etemu/wilssen/core/PCB/temp/microSD_pin.png

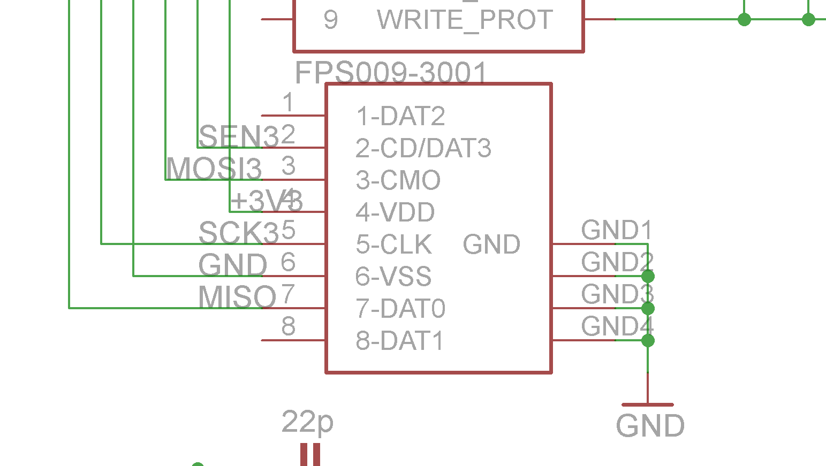
core/PCB/temp/microSD_pin.png
