etemu/wilssen/core/PCB/Wilssen_core_v0.201a.brd.png

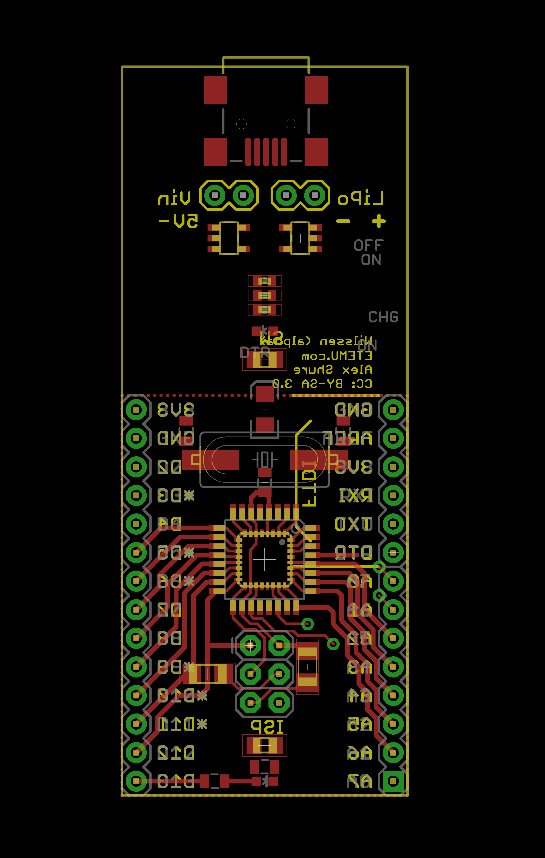
core/PCB/Wilssen_core_v0.201a.brd.png
