etemu/wilssen/core/PCB/Wilssen_core_v0.203a.brd.png

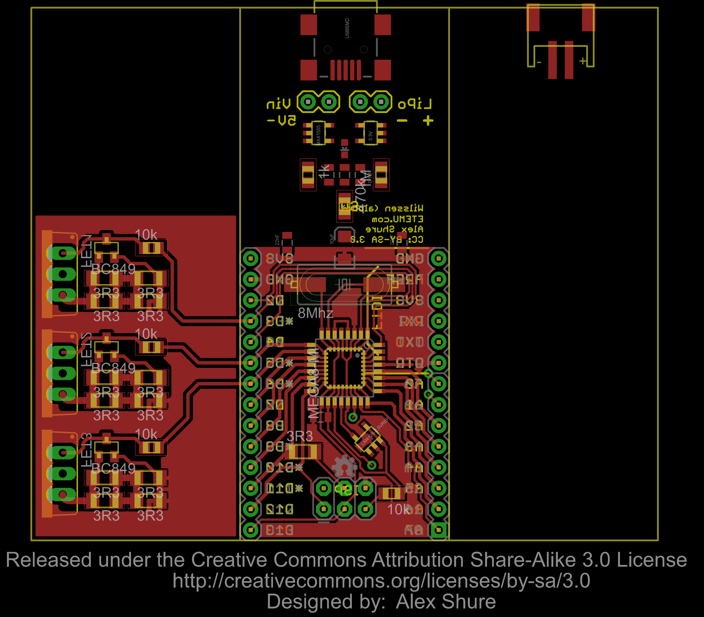
core/PCB/Wilssen_core_v0.203a.brd.png
