etemu/wilssen/core/PCB/Wilssen_core_v0.203a.brd_detail.png

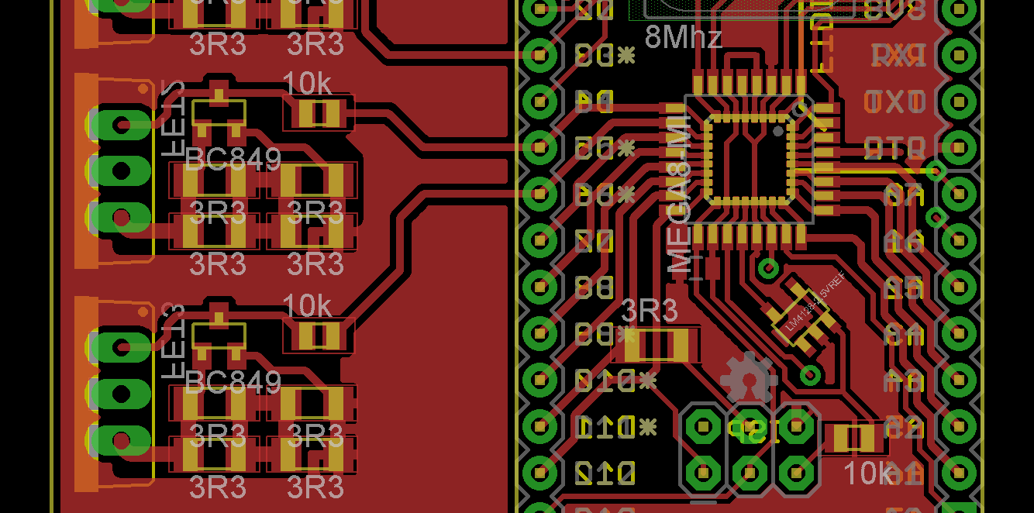
core/PCB/Wilssen_core_v0.203a.brd_detail.png
