etemu/wilssen/core/PCB/Wilssen_core_v0.203a.sch.png

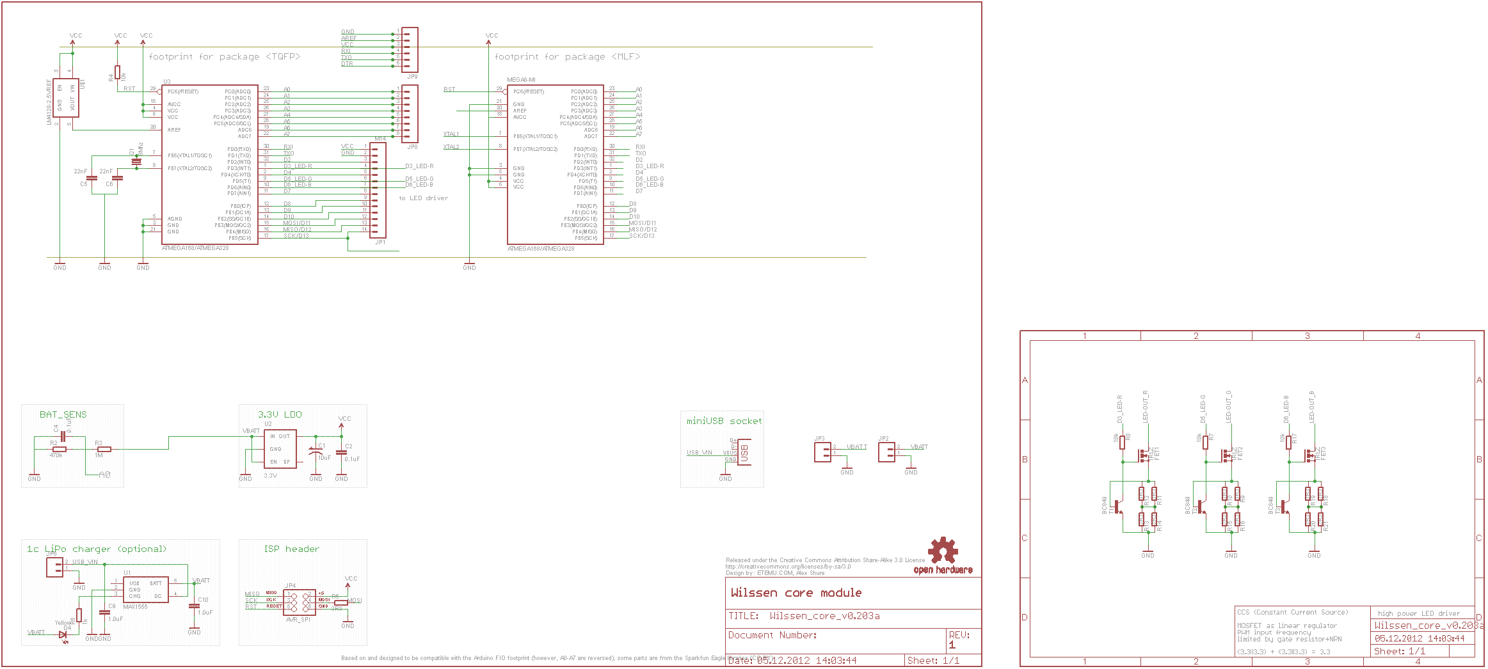
core/PCB/Wilssen_core_v0.203a.sch.png
