etemu/wilssen/core/PCB/Wilssen_core_v0.204a.brd.png

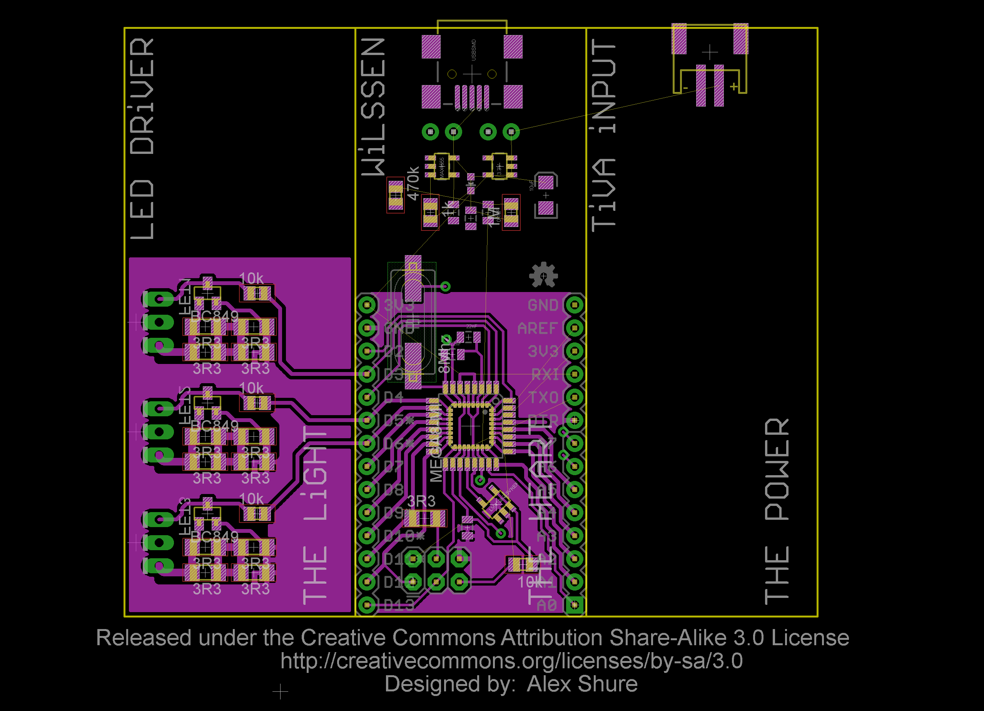
core/PCB/Wilssen_core_v0.204a.brd.png
