etemu/wilssen/core/PCB/Wilssen_core_v0.204a.brd_detail.png

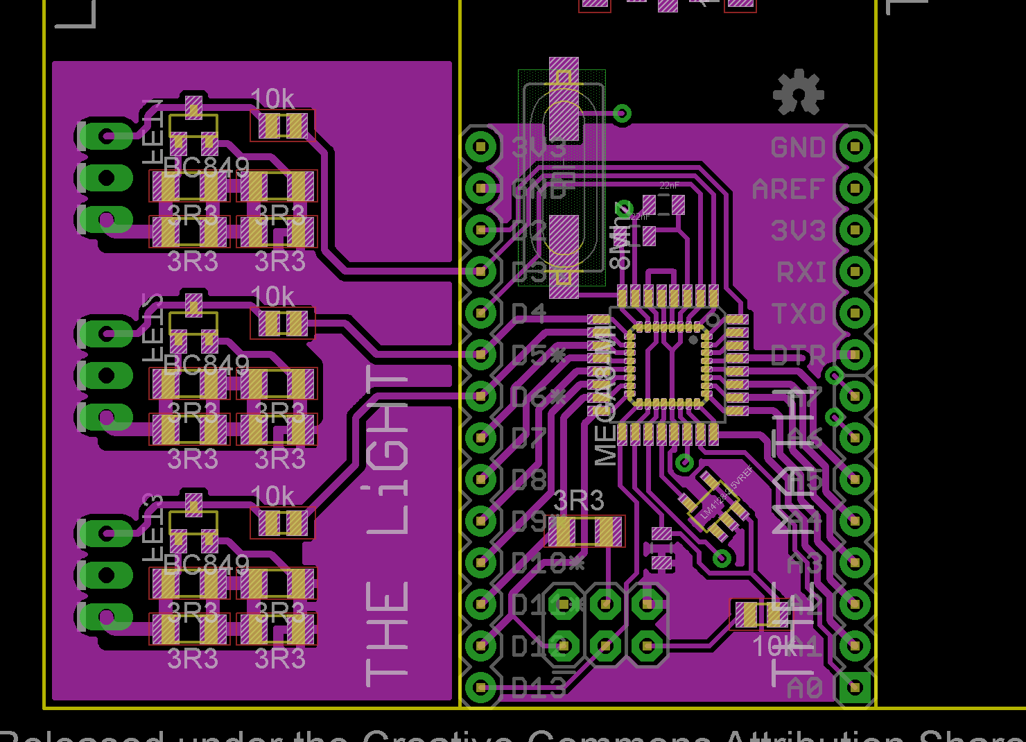
core/PCB/Wilssen_core_v0.204a.brd_detail.png
