etemu/wilssen/core/PCB/Wilssen_core_v0.206a.brd.png

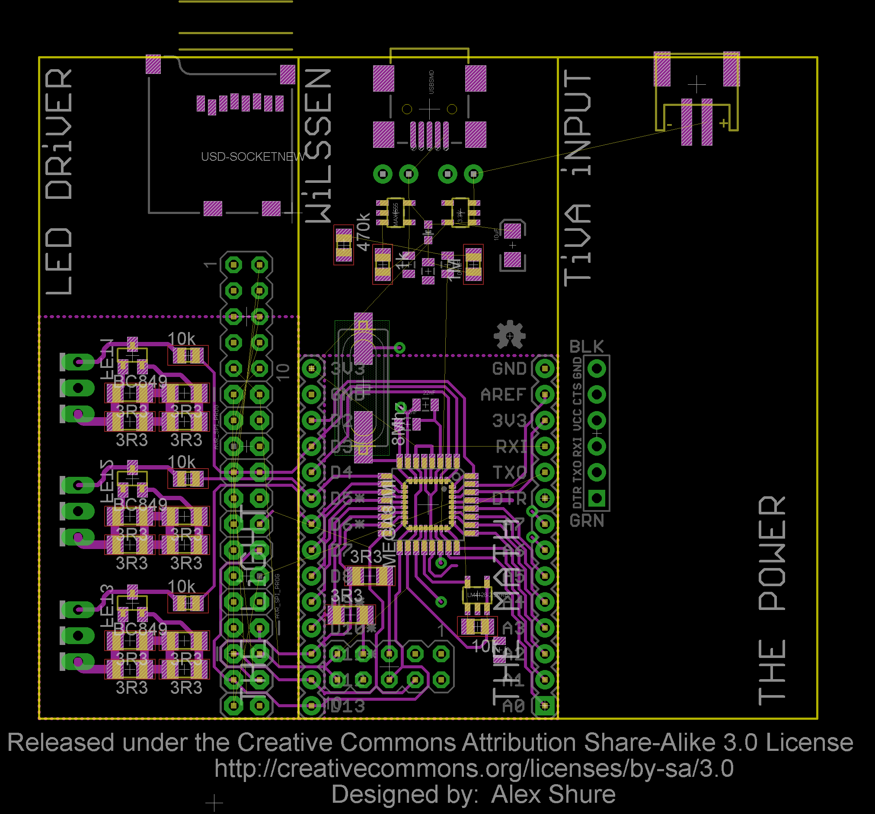
core/PCB/Wilssen_core_v0.206a.brd.png
