etemu/wilssen/core/PCB/Wilssen_core_v0.209a.brd.png

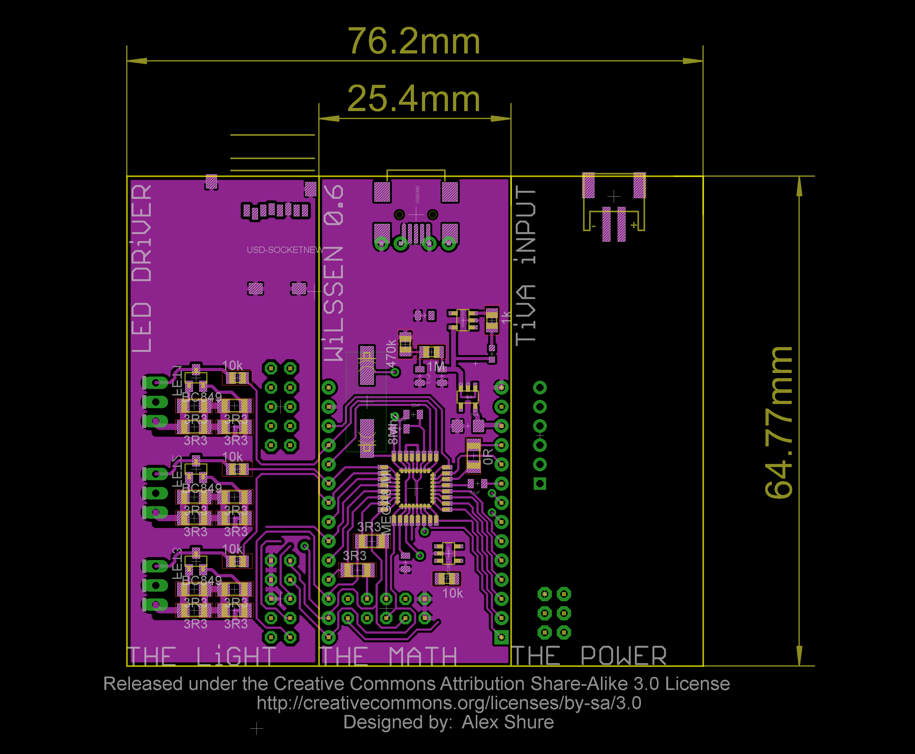
core/PCB/Wilssen_core_v0.209a.brd.png
