etemu/wilssen/core/PCB/Wilssen_core_v0.215a.brd.png

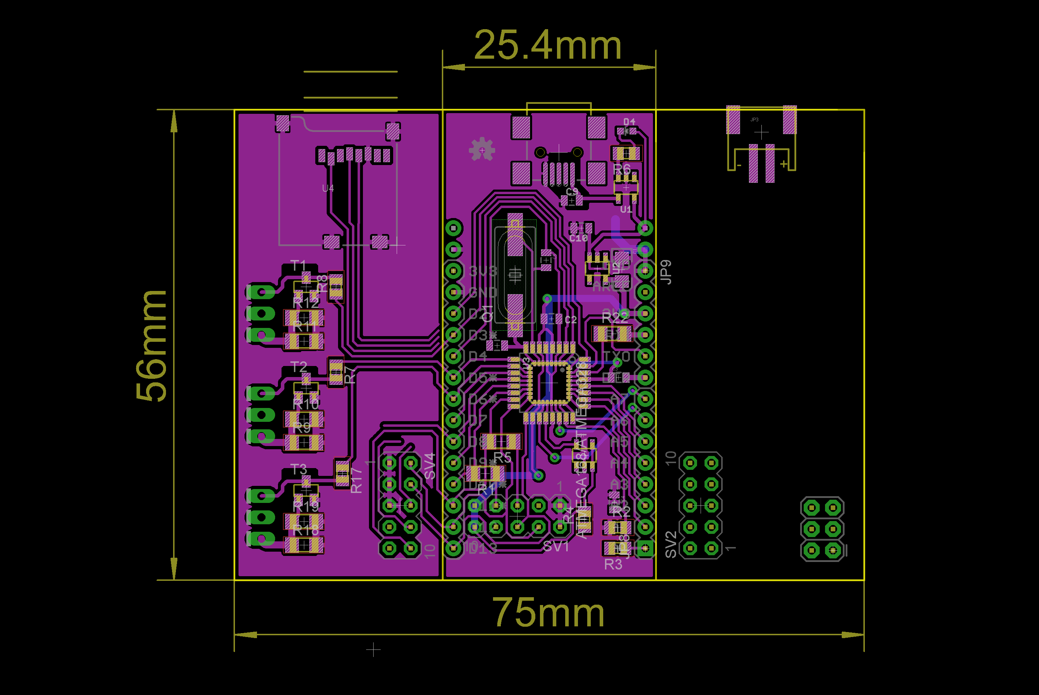
core/PCB/Wilssen_core_v0.215a.brd.png
