etemu/wilssen/core/PCB/Wilssen_core_v0.215a_2.brd.png

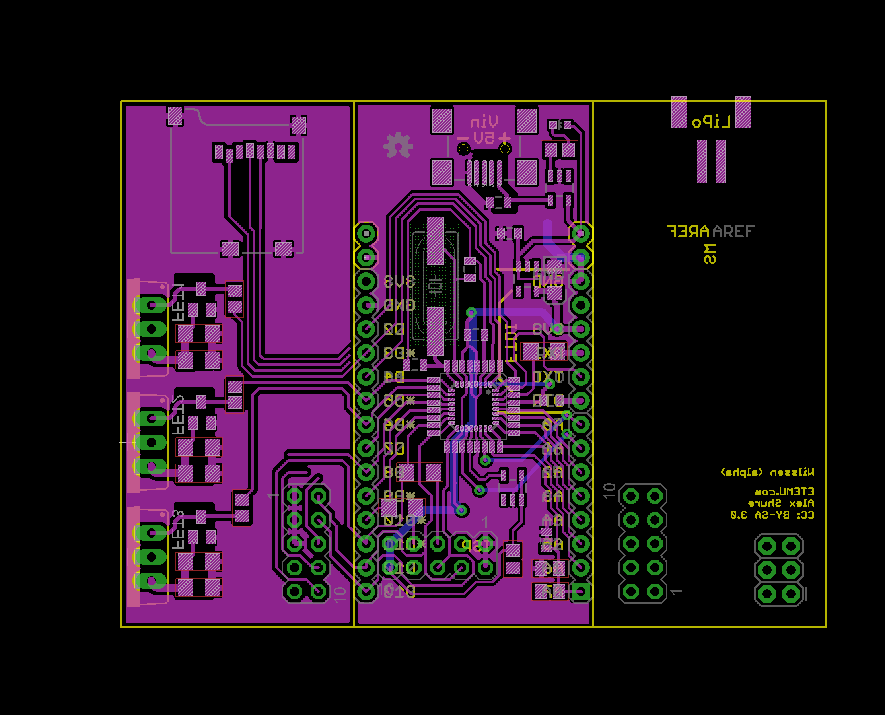
core/PCB/Wilssen_core_v0.215a_2.brd.png
