etemu/wilssen/core/PCB/Wilssen_core_v0.216a.brd.png

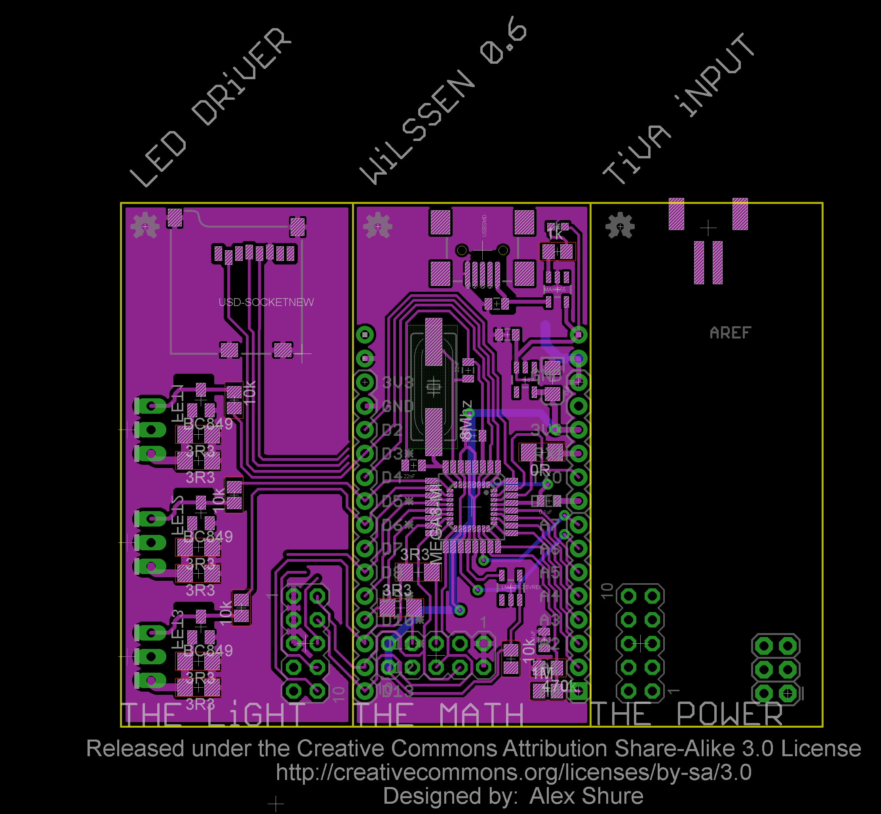
core/PCB/Wilssen_core_v0.216a.brd.png
