etemu/wilssen/software/RGBlink/RGBlink.cpp

#if defined(ARDUINO) && ARDUINO >= 100 //check if using Arduino or Wiring
  #include "Arduino.h"
#else
  #include "WProgram.h"
#endif

#include "RGBlink.h"

/* 
 * Modes:
 * 0 Color
 * 1 Pattern
 * 2 Heartbeat
 * 3 Selftest
 */

/***************************
 * Initialization
 ***************************/


LED::LED(uint8_t to_red_pin,uint8_t to_green_pin,uint8_t to_blue_pin) // init the LED w/out setting the inverted param
{
	red_pin = to_red_pin;
	green_pin = to_green_pin;
	blue_pin = to_blue_pin;
    
	initDefaults();

	inverted = false;
}

LED::LED(uint8_t to_red_pin,uint8_t to_green_pin,uint8_t to_blue_pin,bool to_inverted) // init the LED w/ setting the inverted param
{
	red_pin = to_red_pin;
	green_pin = to_green_pin;
	blue_pin = to_blue_pin;
    
    initDefaults();

	inverted = to_inverted;    
}
void LED::initDefaults()
{
	isOn = true;
	setColor(red);
    
	blink_on = 1000;  // basic blink pattern (1 sec off/1 sec on)
	blink_off = 1000;
	mode = 0;

	prevMillis = 0;
}

/***************************
 * Basic operations
 ***************************/


void LED::on()
{
	isOn = true;
	writeHSB(color);
}

void LED::off()
{
	isOn = false;

	writeRGB((RGB){0,0,0});
}

/***************************
 * update cycle for patterns
 ***************************/

void LED::update()
{
	switch(mode)
	{	
		case 1: //blink
		{
			uint16_t blink_diff = (uint16_t)(millis() - prevMillis);
		   	if(isOn && blink_diff >= blink_on)//blink_on)  // a boolean 'true' equals '1', 'false' equals '0'
		   	{
		   		off();
		   		prevMillis = millis();
		   	}

		   	else if(!isOn && blink_diff >= blink_off)//blink_off)  // a boolean 'true' equals '1', 'false' equals '0'
		   	{
		   		on();
		   		prevMillis = millis();
		   	}
			break;
		}	

		case 2: //fade
		{
			uint16_t blink_diff = (uint16_t)(millis() - prevMillis);

			if(isOn)
		   	{
		   		float perc = (float)blink_diff / (float)blink_on;
		   		if(perc >= 1)
		   		{ 
		   			isOn = false;
		   			prevMillis = millis();
		   		}
		   		else
		   		{
		   			HSB newCol = {color.hue,color.sat,(uint8_t)(perc*color.bri)};
		   			writeHSB(newCol);
		   		}
		   	}

		   	else if(!isOn)
		   	{
		   		float perc = (float)blink_diff / (float)blink_off;

		   		if(perc >= 1)
		   		{ 
		   			isOn = true;
		   			prevMillis = millis();
		   		}
		   		else
		   		{
		   			HSB newCol = {color.hue,color.sat,255-(uint8_t)(perc*color.bri)};
		   			writeHSB(newCol);
		   		}
		   		
		   	}
		   	
			break;	
		}

		case 3: //selftest
		{
			uint16_t blink_diff = (uint16_t)(millis() - prevMillis);

			writeHSB((HSB){(blink_diff/10)%360,255,255});
		   	
		   	if (blink_diff>=3600)
		   	{
		   		setMode(0);
		   	}
			break;	
		}


		case 4: //flash
		{	
			uint16_t blink_diff = (uint16_t)(millis() - prevMillis);
		   	if(isOn && blink_diff >= flash_on) 
		   	{
		   		off();
		   		setMode(0);
		   	}
		   	break;
		}

		//default:
	    	//do nothing
	}
}

/***************************
 *	Setter/Getter methods
 ***************************/

 void LED::setBlink(uint16_t to_on_val, uint16_t to_off_val)
{
	blink_off = to_off_val;
	blink_on =	to_on_val;
}

 void LED::flash(uint16_t to_on_val)
{
	flash_on = to_on_val; 
	on();
	setMode(4);
}

void LED::writeRGB(RGB to_color)  // show a color w/out deleting the buffer, needed for fading
{
	if(inverted)
	{
		analogWrite(red_pin, ~to_color.red);    // "~" is a bitshift operator and will invert the given value (255->0,100->155)
		analogWrite(green_pin, ~to_color.green);
		analogWrite(blue_pin, ~to_color.blue);		
	}
	else
	{   
		analogWrite(red_pin, to_color.red);
		analogWrite(green_pin, to_color.green);
		analogWrite(blue_pin, to_color.blue);
	}
}

void LED::writeHSB(HSB to_color)  // show a color w/out deleting the buffer, needed for fading
{
	writeRGB(HSBtoRGB(to_color));	
}

void LED::setColor(HSB to_color)
{
	color = to_color;
	if (isOn && mode == 0) // prevent performance issues when fading while setting color 
		writeHSB(color);
}

void LED::setMode(uint8_t to_mode)
{
	if(mode != to_mode)
	{
		mode = to_mode;
		prevMillis = millis();
	}
}

int LED::getMode()
{
	return mode;
}


HSB mix(HSB color_1, HSB color_2, uint8_t step)
{
	float perc = (float)step/255;

	HSB newCol = {(uint8_t)((1-perc)*color_1.hue)	+ (uint8_t)((perc)*color_2.hue),
		   		  (uint8_t)((1-perc)*color_1.sat)	+ (uint8_t)((perc)*color_2.sat),
		   		  (uint8_t)((1-perc)*color_1.bri)	+ (uint8_t)((perc)*color_2.bri)};

	return newCol;
}

RGB HSBtoRGB(HSB from_color) 
{ 
	/*
	 * Hue: 0..359
	 * Sat: 0..255
	 * bri: 0..255
	 */

	RGB result;
 	from_color.bri = pgm_read_byte(&dim_curve[from_color.bri]);
 	from_color.sat = 255-pgm_read_byte(&dim_curve[255-from_color.sat]);

	uint8_t r, b, g, base;

  	if (from_color.sat == 0) //Acromatic, from_color.hue not needed
  	{ 
    	result.red = from_color.bri;
	    result.green = from_color.bri;
	    result.blue = from_color.bri; 
	} 
	else  
	{ 
		base = ((255 - from_color.sat) * from_color.bri)>>8;

	    switch(from_color.hue/hstep) 
	    { 
		    case 0://red
		    {
		        result.red = from_color.bri;		
		        result.green = (((from_color.bri-base)*from_color.hue)/hstep)+base;		
		        result.blue = base;		
		    	break;
			}

		    case 1://yellow
		    {
		        result.red = (((from_color.bri-base)*(hstep-(from_color.hue%hstep)))/hstep)+base;		
		        result.green = from_color.bri;		
		        result.blue = base;		
		    	break;
		    }

		    case 2://green
		    {
		        result.red = base;		
		        result.green = from_color.bri;		
		        result.blue = (((from_color.bri-base)*(from_color.hue%hstep))/hstep)+base;		
		    	break;
			}

			case 3://cyan
		    {
		        result.red = base;		
		        result.green = (((from_color.bri-base)*(hstep-(from_color.hue%hstep)))/hstep)+base;		
		        result.blue = from_color.bri;		
		    	break;
		    }

			case 4://blue
		    {
		        result.red = (((from_color.bri-base)*(from_color.hue%hstep))/hstep)+base;		
		        result.green = base;		
		        result.blue = from_color.bri;		
		    	break;
		    }

			case 5://magenta
		    {
		        result.red = from_color.bri;		
		        result.green = base;		
		        result.blue = (((from_color.bri-base)*(hstep-(from_color.hue%hstep)))/hstep)+base;		
		    	break;
		    }		
		}
	}   
	return result;
}
